z3r0nightmare/kiki-Keyboard/Firmware/vial-qmk-code/keymaps/oled.c

#include <stdio.h>
#include <stdlib.h>
#include <stdbool.h>
#include "quantum.h"

#define IDLE_FRAMES 5
#define IDLE_SPEED 30
#define TAP_FRAMES 2
#define TAP_SPEED 40
#define ANIM_FRAME_DURATION 150 
#define ANIM_SIZE 512

char wpm_str[10];
uint32_t anim_timer = 0;
uint32_t anim_sleep = 0;
uint8_t current_idle_frame = 0;
uint8_t current_tap_frame = 0;
static long int oled_timeout = 60000; 

oled_rotation_t oled_init_user(oled_rotation_t rotation) {
    return OLED_ROTATION_0; 
}

// This captures the keypress
static char last_key_str[10] = "K:None";

void set_keylog(uint16_t keycode, keyrecord_t *record) {
    if (record->event.pressed) {
        last_key_str[0] = '\0'; // Clear the string
        
        // If it's a normal letter/number
        if (keycode >= KC_A && keycode <= KC_Z) {
            sprintf(last_key_str, "K:%c", (keycode - KC_A + 'A'));
        } else if (keycode >= KC_0 && keycode <= KC_9) {
            sprintf(last_key_str, "K:%c", (keycode - KC_0 + '0'));
        } else {
            // For symbols/modifiers, just show the hex code to save space
            sprintf(last_key_str, "K:%02X", keycode & 0xFF);
        }
    }
}

static void render_status(void) {
    // Line 1: WPM (Top Left)
    sprintf(wpm_str, "W:%03d", get_current_wpm());
    oled_write(wpm_str, false);

    // Line 2: Layer (Below WPM)
    oled_set_cursor(0, 1); 
    switch (get_highest_layer(layer_state)) {
        case 3:  oled_write_P(PSTR("ADJ"), false); break;
        case 2:  oled_write_P(PSTR("RAI"), false); break;
        case 1:  oled_write_P(PSTR("LOW"), false); break;
        default: oled_write_P(PSTR("BASE"), false); break;
    }

    // Line 3: Last Key (Below Layer)
    oled_set_cursor(0, 2);
    oled_write(last_key_str, false);
}
static void render_anim(void) {
    static const char PROGMEM idle[IDLE_FRAMES][ANIM_SIZE] = {
        {0,0,0,0,0,0,0,0,0,0,0,0,0,0,0,0,0,0,0,0,0,0,0,0,0,0,0,0,0,0,0,0,0,0,0,0,0,0,0,0,0,0,0,0,0,0,0,0,0,0,0,0,0,0,0,0,0,0,128,64,64,32,32,32,32,16,16,16,16,16,8,8,4,4,4,8,48,64,128,0,0,0,0,0,0,0,0,0,0,0,0,0,0,0,0,0,0,0,0,0,0,0,0,0,0,0,0,0,0,0,0,0,0,0,0,0,0,0,0,0,0,0,0,0,0,128,128,128,0,0,0,0,0,0,0,0,0,0,0,0,0,0,0,0,0,0,0,0,0,0,0,0,0,0,0,0,0,0,0,0,0,0,0,0,0,0,0,0,0,0,0,0,0,0,0,0,0,24,100,130,2,2,2,2,2,1,0,0,0,0,128,128,0,0,0,0,0,0,0,0,0,128,0,48,48,0,192,193,193,194,4,8,16,32,64,128,0,0,0,128,128,128,128,64,64,64,64,32,32,32,32,16,16,16,16,8,8,8,8,8,4,4,4,4,4,2,2,2,2,1,1,1,1,0,0,0,0,0,0,0,0,0,0,0,0,0,0,0,0,0,0,0,0,0,0,0,0,0,0,0,0,0,0,0,0,0,0,0,0,0,0,0,0,0,0,0,0,0,0,0,0,0,0,0,192,56,4,3,0,0,0,0,0,0,0,12,12,12,13,1,0,64,160,33,34,18,17,17,17,9,8,8,8,8,4,4,8,8,16,16,16,16,16,17,15,1,1,0,0,0,0,0,0,0,0,0,0,0,0,0,0,0,0,0,0,0,0,0,0,0,0,0,0,0,0,0,0,0,0,0,0,0,0,0,0,0,0,0,0,0,0,0,0,0,0,0,0,0,0,0,0,128,128,128,128,128,64,64,64,64,64,32,32,32,32,32,16,16,16,16,16,8,8,8,8,8,4,4,4,4,4,2,3,2,2,1,1,1,1,1,1,2,2,4,4,8,8,8,8,8,7,0,0,0,0,0,0,0,0,0,0,0,0,0,0,0,0,0,0,0,0,0,0,0,0,0,0,0,0,0,0,0,0,0,0,0,0,0,0,0,0,0,0,0,0,0,0,0,0,0,0,0,0,0,0,0,0,0,0,0,0,0},
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
            oled_write_raw_P(prep[0], ANIM_SIZE);
        }
        if (get_current_wpm() >= TAP_SPEED) {
            current_tap_frame = (current_tap_frame + 1) % TAP_FRAMES;
            oled_write_raw_P(tap[abs((TAP_FRAMES - 1) - current_tap_frame)], ANIM_SIZE);
        }
    }

    if (get_current_wpm() != 0) {
        oled_on();
        if (timer_elapsed32(anim_timer) > ANIM_FRAME_DURATION) {
            anim_timer = timer_read32();
            animation_phase();
        }
        anim_sleep = timer_read32();
    } else {
        if (timer_elapsed32(anim_sleep) > oled_timeout) {
            oled_off();
        } else {
            if (timer_elapsed32(anim_timer) > ANIM_FRAME_DURATION) {
                anim_timer = timer_read32();
                animation_phase();
            }
        }
    }
}
bool oled_task_user(void) {
    // Reset cursor to top-left for BOTH
    oled_set_cursor(0, 0);
    
    // Draw the cat first (background)
    render_anim();
    
    // Set cursor back to top-left to draw text over the cat
    oled_set_cursor(0, 0);
    render_status();

    return false;
}
